ThinkOffApp/WhereWatch/cad/pendant-preview.png

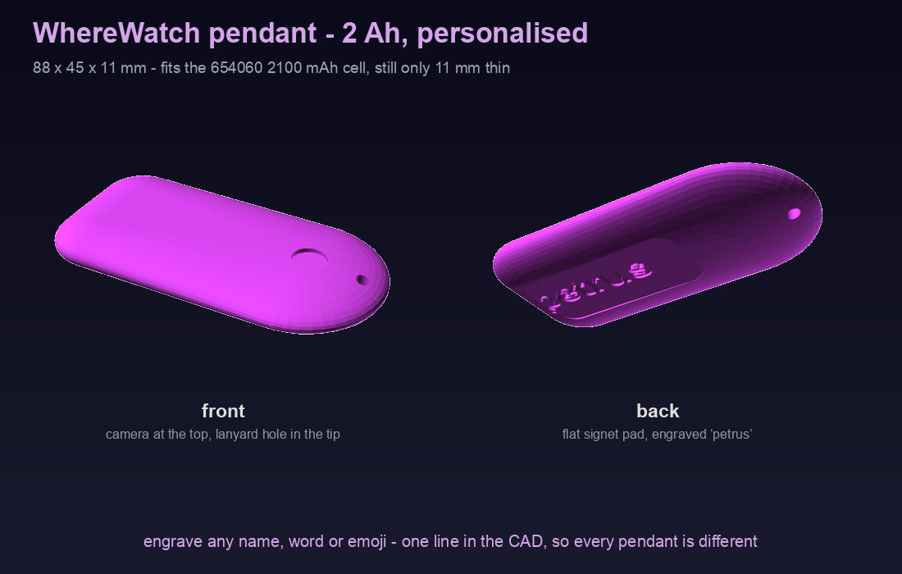
cad/pendant-preview.png
