ThinkOffApp/WhereWatch/firmware/matrix/heart/heart-v1-preview.png

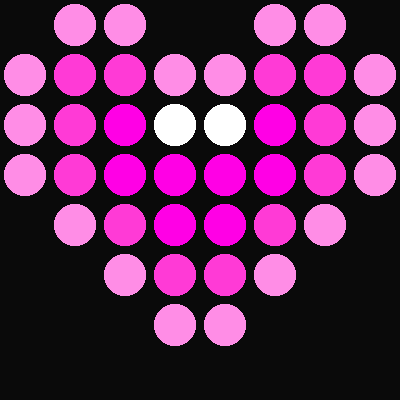
firmware/matrix/heart/heart-v1-preview.png
